OLIMEX/ESP32-S2-DevKit-LiPo-USB/HARDWARE/ESP32-S2-DevKit-USB-Rev-B/3d/BAT54.step

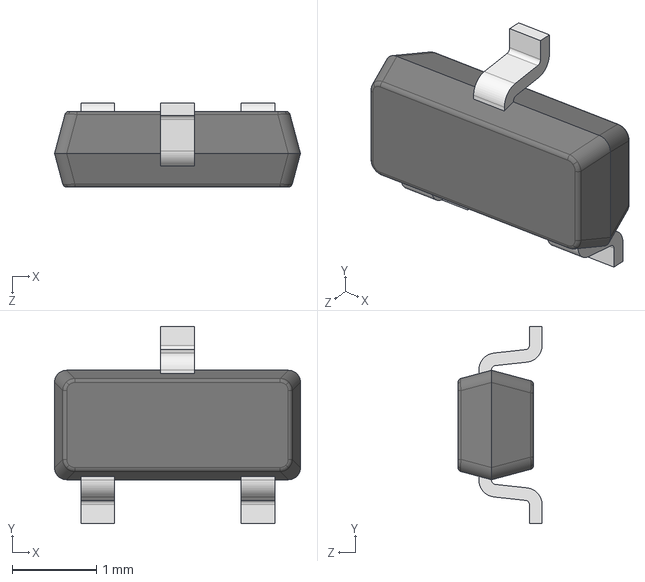
[picture p15: CAD file, 2021-02-18]
HARDWARE/ESP32-S2-DevKit-USB-Rev-B/3d/BAT54.step
2.92 x 2.34 x 1.00 mm
